crimeofheart/QIDI-X-MAX-Motherboard/Firmware files/18_02_2021 read from SWD connector/Fuses.JPG

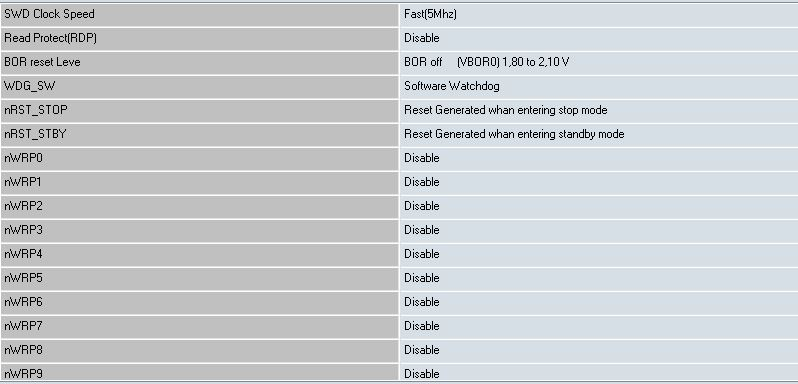
Firmware files/18_02_2021 read from SWD connector/Fuses.JPG
