crimeofheart/QIDI-X-MAX-Motherboard/Images/SWD connector for programming.jpg

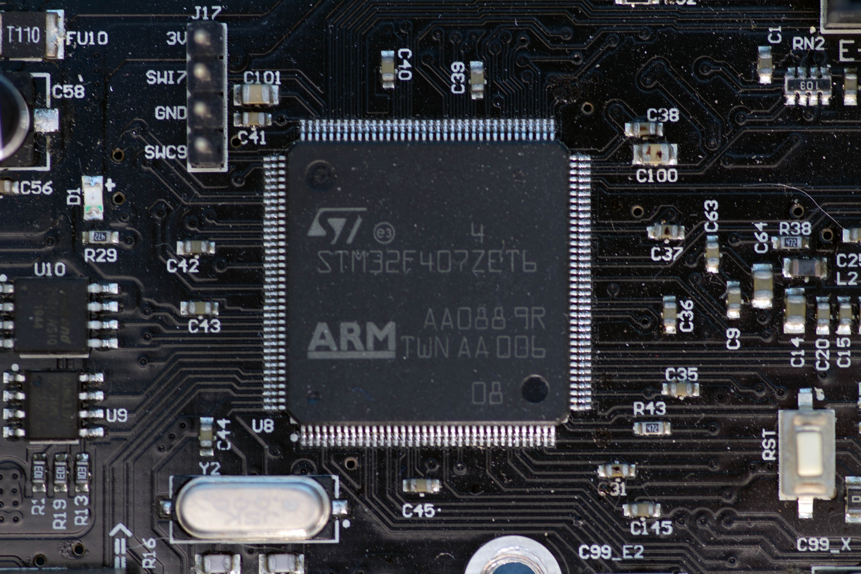
Images/SWD connector for programming.jpg
