crimeofheart/QIDI-X-MAX-Motherboard/Images/WIFI module.png

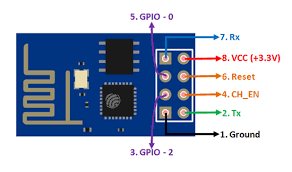
Images/WIFI module.png
